luftek/LimeSDR-USB/hardware/enclosure/0v5_76x35_+4conn/images/design/2016-08-19 16_58_33-Pcbnew (2016-07-22 BZR 6991, Git 146a78a)-product C__Users_Borec_Documents_GitHu.png

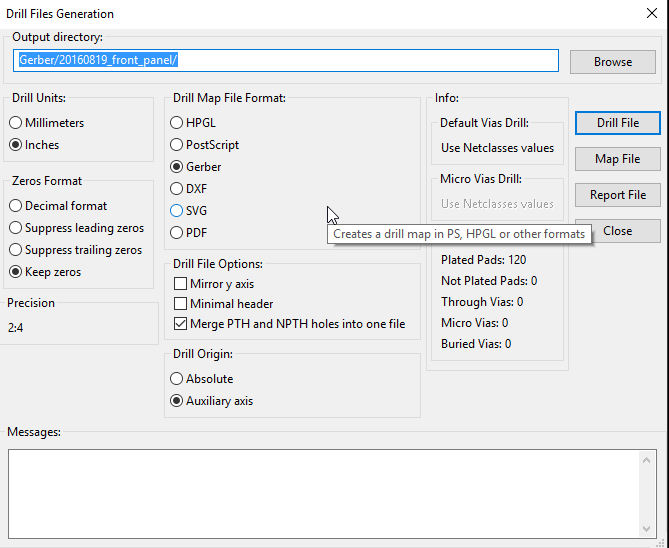
hardware/enclosure/0v5_76x35_+4conn/images/design/2016-08-19 16_58_33-Pcbnew (2016-07-22 BZR 6991, Git 146a78a)-product C__Users_Borec_Documents_GitHu.png
