luftek/LimeSDR-USB/hardware/enclosure/0v5_76x35_+4conn/images/design/2016-09-24_17_06_20-Greenshot_capture_form.png

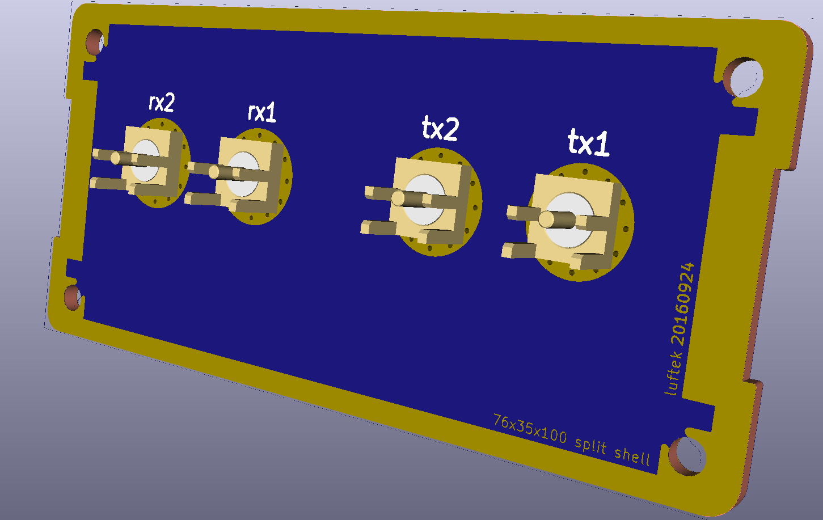
hardware/enclosure/0v5_76x35_+4conn/images/design/2016-09-24_17_06_20-Greenshot_capture_form.png
