luftek/LimeSDR-USB/hardware/enclosure/0v5_76x35_+4conn/images/design/2016-09-24_17_07_21-3D_Viewer.png

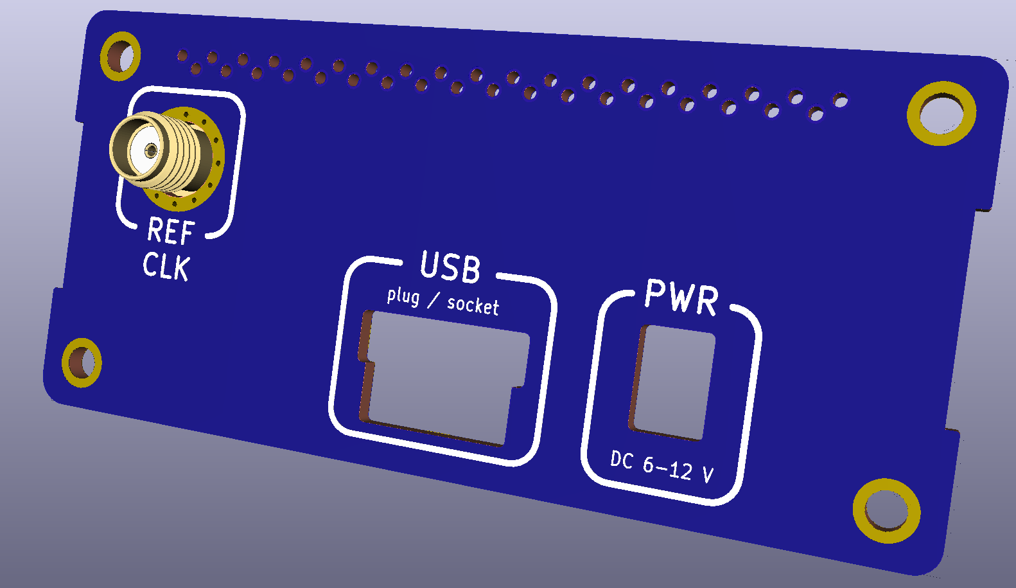
hardware/enclosure/0v5_76x35_+4conn/images/design/2016-09-24_17_07_21-3D_Viewer.png
