luftek/LimeSDR-USB/hardware/enclosure/0v5_76x35_+4conn/images/design/2016-09-25 17_21_54-Program Manager.png

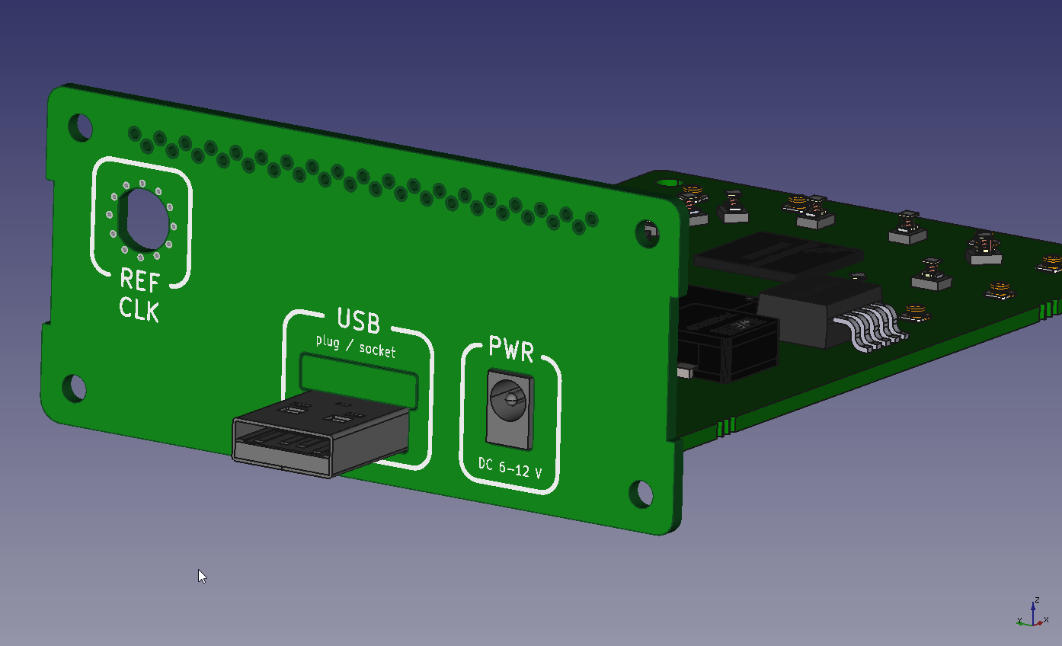
hardware/enclosure/0v5_76x35_+4conn/images/design/2016-09-25 17_21_54-Program Manager.png
