luftek/LimeSDR-USB/hardware/enclosure/0v5_76x35_+4conn/images/design/2016-09-25 18_22_17-FreeCAD.png

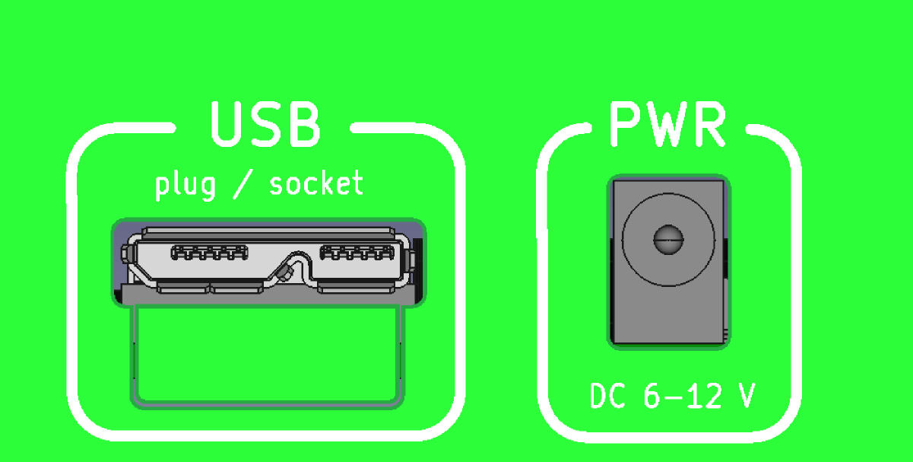
hardware/enclosure/0v5_76x35_+4conn/images/design/2016-09-25 18_22_17-FreeCAD.png
