luftek/LimeSDR-USB/hardware/enclosure/0v5_76x35_+4conn/images/design/20160924_combined_Combined_Bottom.png

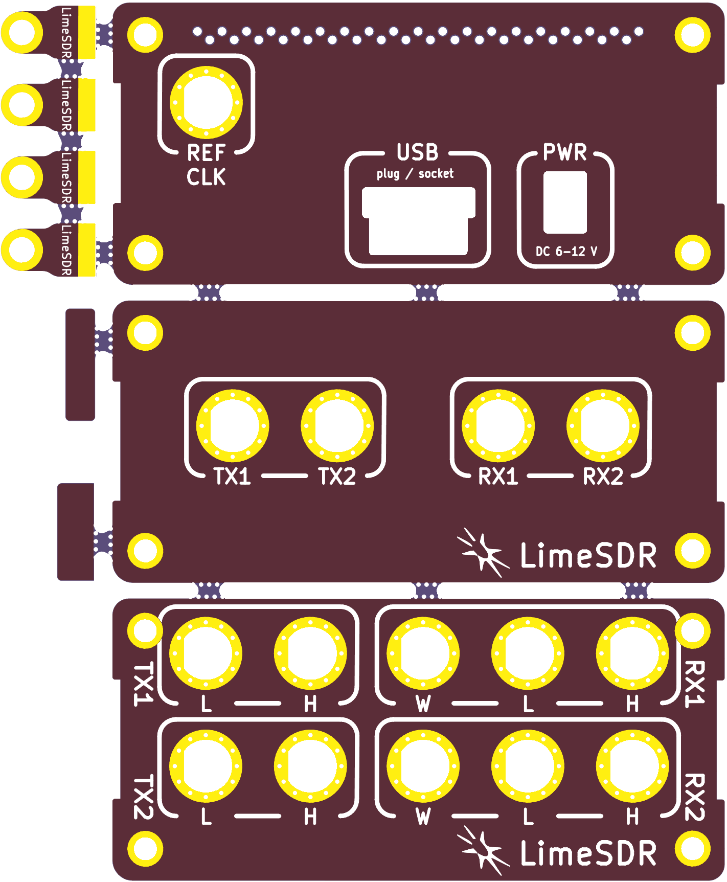
hardware/enclosure/0v5_76x35_+4conn/images/design/20160924_combined_Combined_Bottom.png
