luftek/LimeSDR-USB/hardware/enclosure/0v5_76x35_+4conn/images/design/combined.jpg

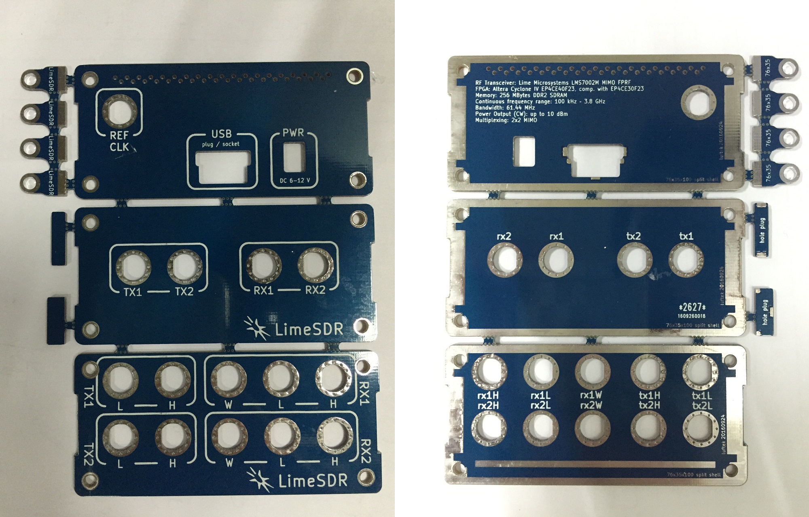
hardware/enclosure/0v5_76x35_+4conn/images/design/combined.jpg
