luftek/LimeSDR-USB/hardware/enclosure/0v5_76x35_+4conn/images/real/0v5_real_3.jpg

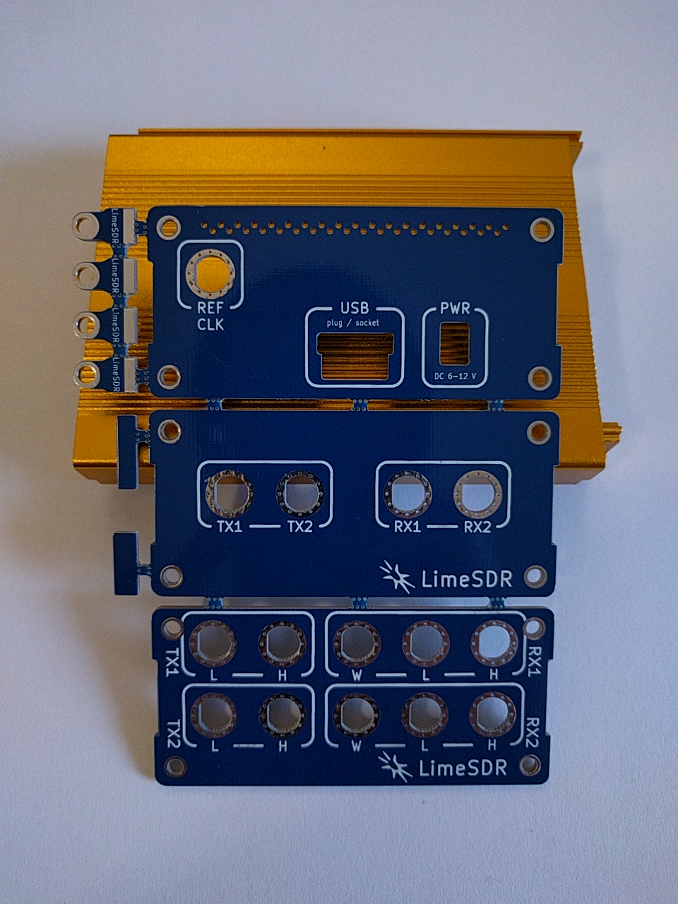
hardware/enclosure/0v5_76x35_+4conn/images/real/0v5_real_3.jpg
