luftek/LimeSDR-USB/hardware/enclosure/0v6_76x35/images/design/2016-10-30 18_30_48-3D Viewer.png

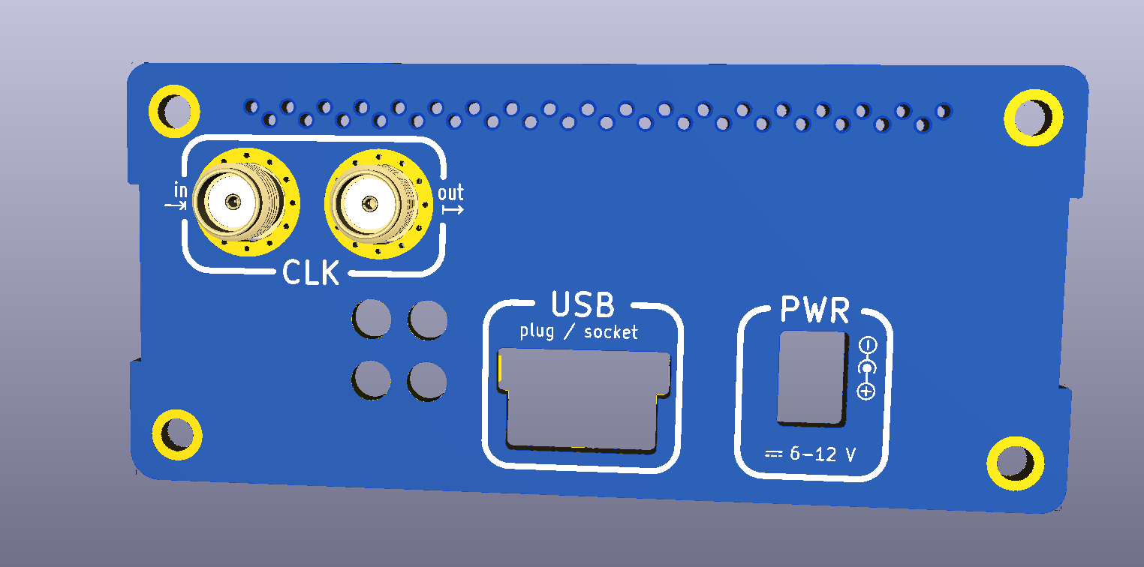
hardware/enclosure/0v6_76x35/images/design/2016-10-30 18_30_48-3D Viewer.png
