luftek/LimeSDR-USB/hardware/enclosure/0v6_76x35/images/real/33045b.JPG

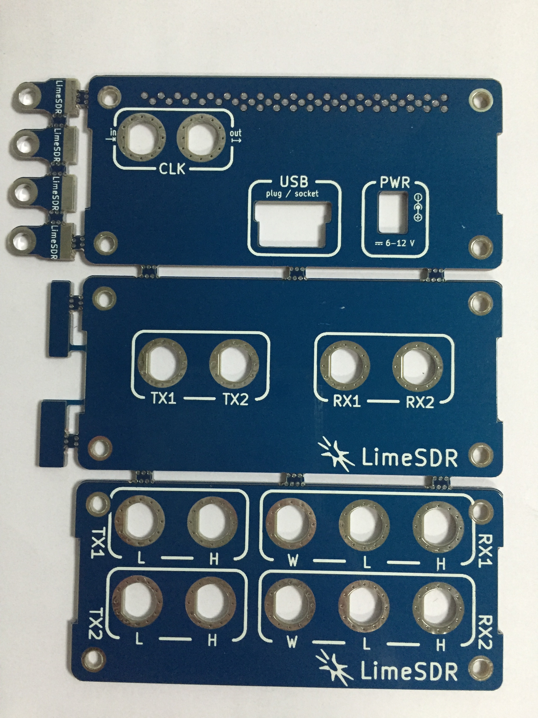
hardware/enclosure/0v6_76x35/images/real/33045b.JPG
