luftek/LimeSDR-USB/hardware/enclosure/0v6_76x35/images/real/35457_0001.jpg

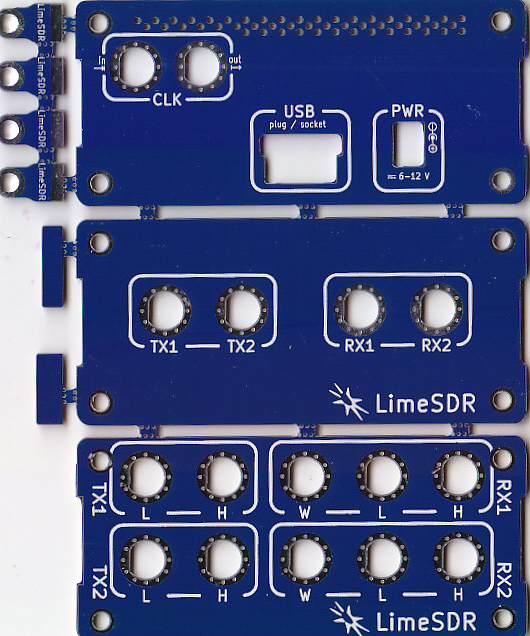
hardware/enclosure/0v6_76x35/images/real/35457_0001.jpg
