luftek/LimeSDR-USB/hardware/enclosure/0v6_76x35/images/real/front.png

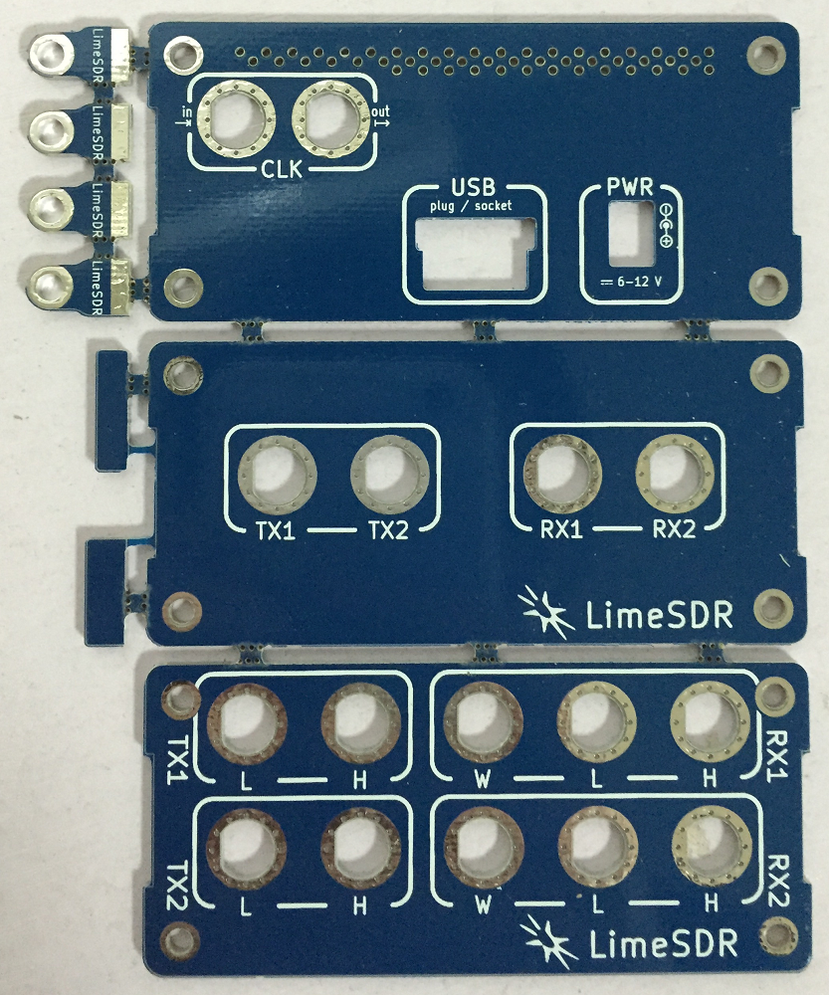
hardware/enclosure/0v6_76x35/images/real/front.png
