luftek/LimeSDR-USB/hardware/enclosure/1v0_76x35_kpl/photos/IMG_20170712_121823.jpg

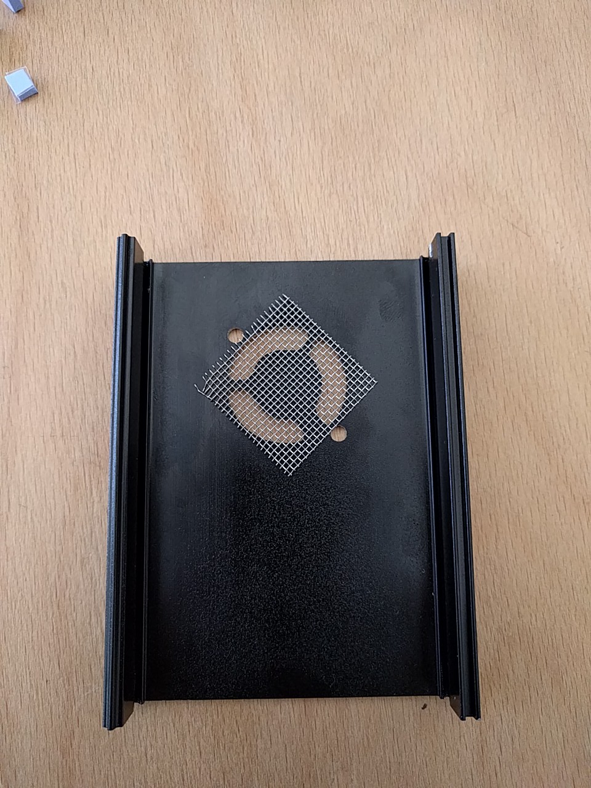
hardware/enclosure/1v0_76x35_kpl/photos/IMG_20170712_121823.jpg
