luftek/LimeSDR-USB/hardware/enclosure/1v0_76x35_kpl/photos/IMG_20170905_221949.jpg

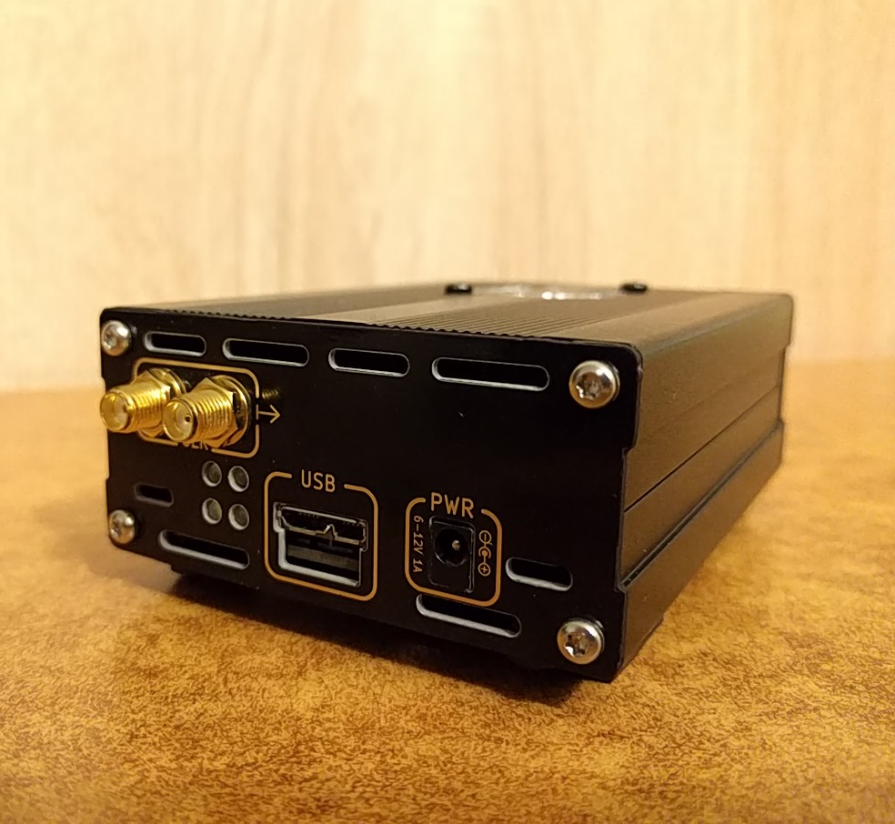
hardware/enclosure/1v0_76x35_kpl/photos/IMG_20170905_221949.jpg
