luftek/LimeSDR-USB/hardware/enclosure/1v0_76x35_kpl/photos/promo/promo.png

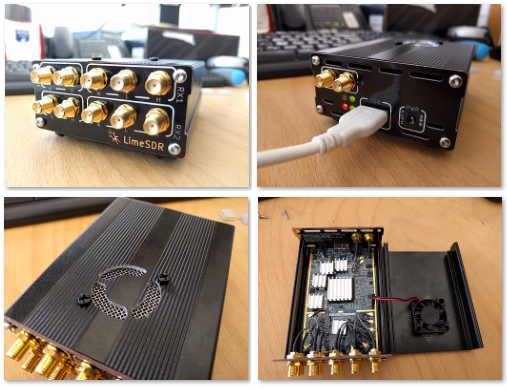
hardware/enclosure/1v0_76x35_kpl/photos/promo/promo.png
