luftek/LimeSDR-USB/hardware/enclosure/0v6_76x35/images/real/Order 2030311.JPG

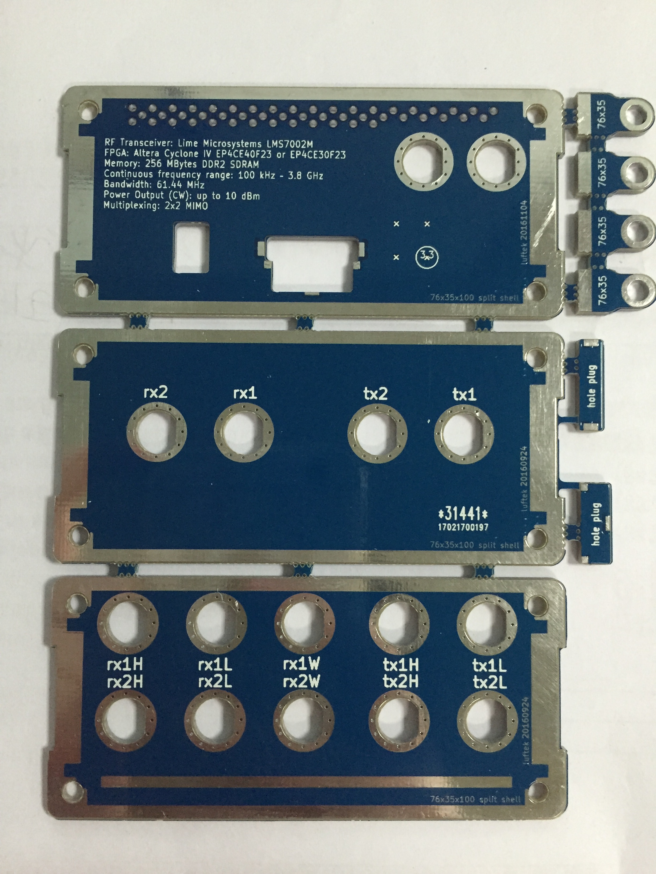
hardware/enclosure/0v6_76x35/images/real/Order 2030311.JPG
