luftek/LimeSDR-USB/hardware/enclosure/1v0_76x35_kpl/photos/instructions/14.jpg

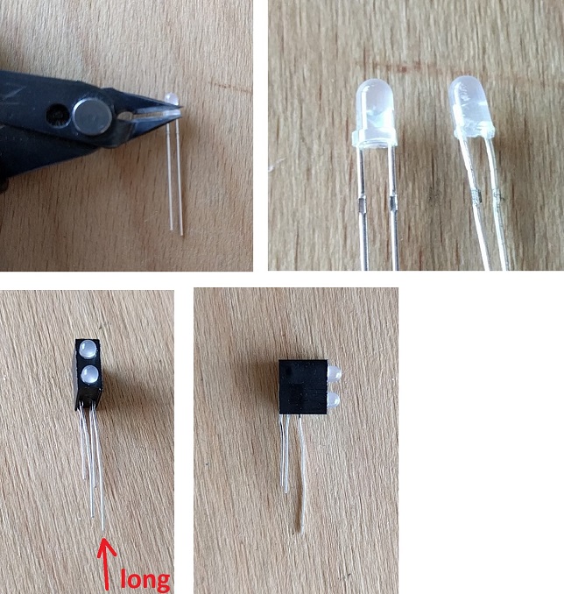
hardware/enclosure/1v0_76x35_kpl/photos/instructions/14.jpg
