luftek/LimeSDR-USB/hardware/enclosure/0v5_76x35_+4conn/issues/#9_Clearance/2016-09-11 12_00_52-AEH050Model.pdf - [H__tuzi_铝型材外壳AEH系列_AEH050 Model (1)] - SumatraPDF.png

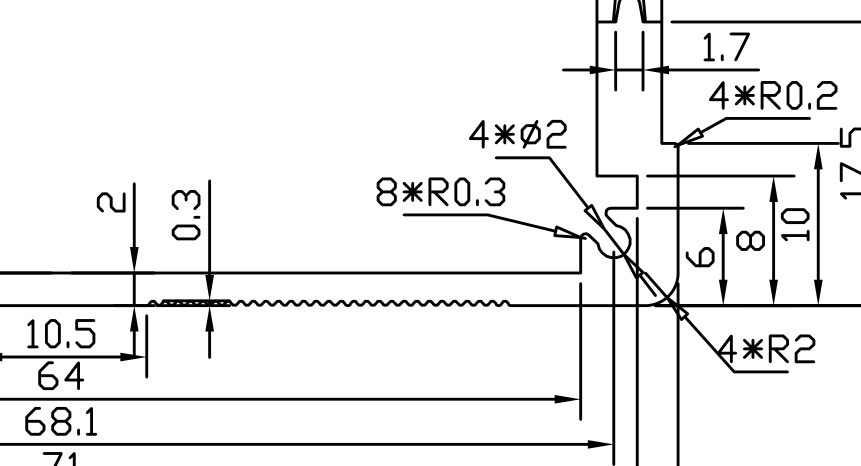
hardware/enclosure/0v5_76x35_+4conn/issues/#9_Clearance/2016-09-11 12_00_52-AEH050Model.pdf - [H__tuzi_铝型材外壳AEH系列_AEH050 Model (1)] - SumatraPDF.png
