luftek/LimeSDR-USB/hardware/enclosure/0v5_76x35_+4conn/issues/#9_Clearance/2016-09-11 12_03_53-No Stock Limesdr Enclosure Front Rear Panel Case Rtl SDR Myriad Hackrf Airspy _ .png

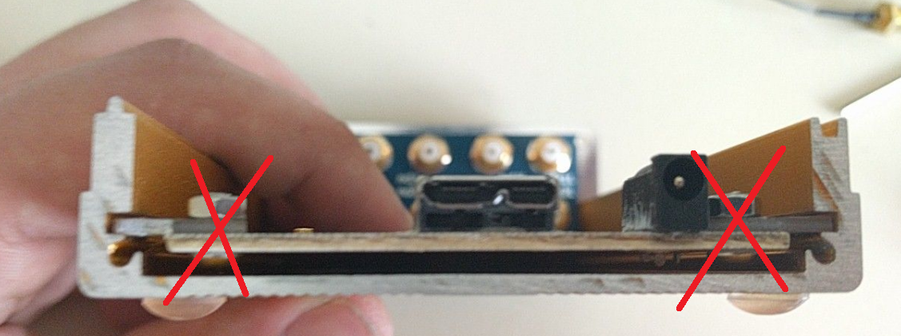
hardware/enclosure/0v5_76x35_+4conn/issues/#9_Clearance/2016-09-11 12_03_53-No Stock Limesdr Enclosure Front Rear Panel Case Rtl SDR Myriad Hackrf Airspy _ .png
