luftek/LimeSDR-USB/hardware/enclosure/0v5_76x35_+4conn/issues/#9_Clearance/2016-09-11 12_47_33-C__Users_Borec_Desktop_bottom_clearance.svg - Inkscape.png

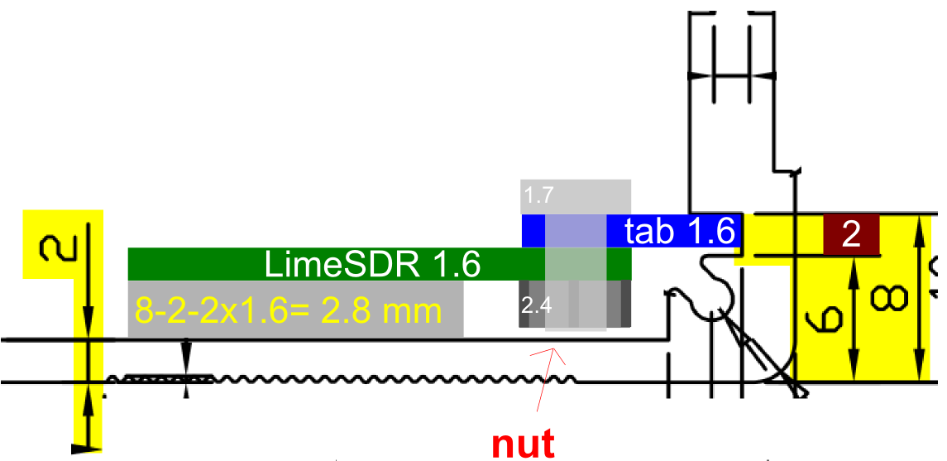
hardware/enclosure/0v5_76x35_+4conn/issues/#9_Clearance/2016-09-11 12_47_33-C__Users_Borec_Desktop_bottom_clearance.svg - Inkscape.png
