luftek/LimeSDR-USB/hardware/enclosure/0v5_76x35_+4conn/issues/#9_Clearance/2016_09_11_12_01_15_AEH050Model.pdf_H_tuzi_铝型材外壳AEH系列_AEH050_Model_1_SumatraPDF.png

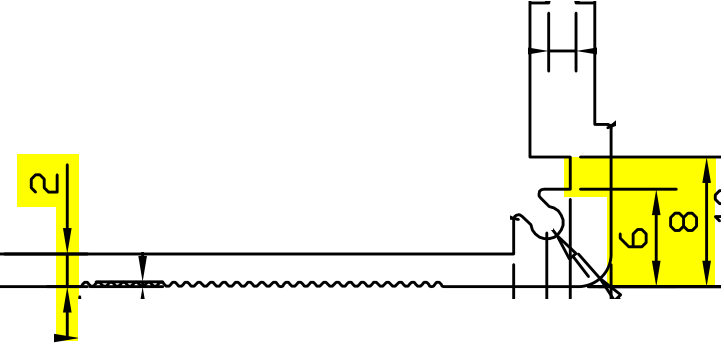
hardware/enclosure/0v5_76x35_+4conn/issues/#9_Clearance/2016_09_11_12_01_15_AEH050Model.pdf_H_tuzi_铝型材外壳AEH系列_AEH050_Model_1_SumatraPDF.png
